MOSH-Insa-Toulouse/2025-2026-4GP-KONIG-EVENSEN/APK_Application/APK_Blocs_Part1.png

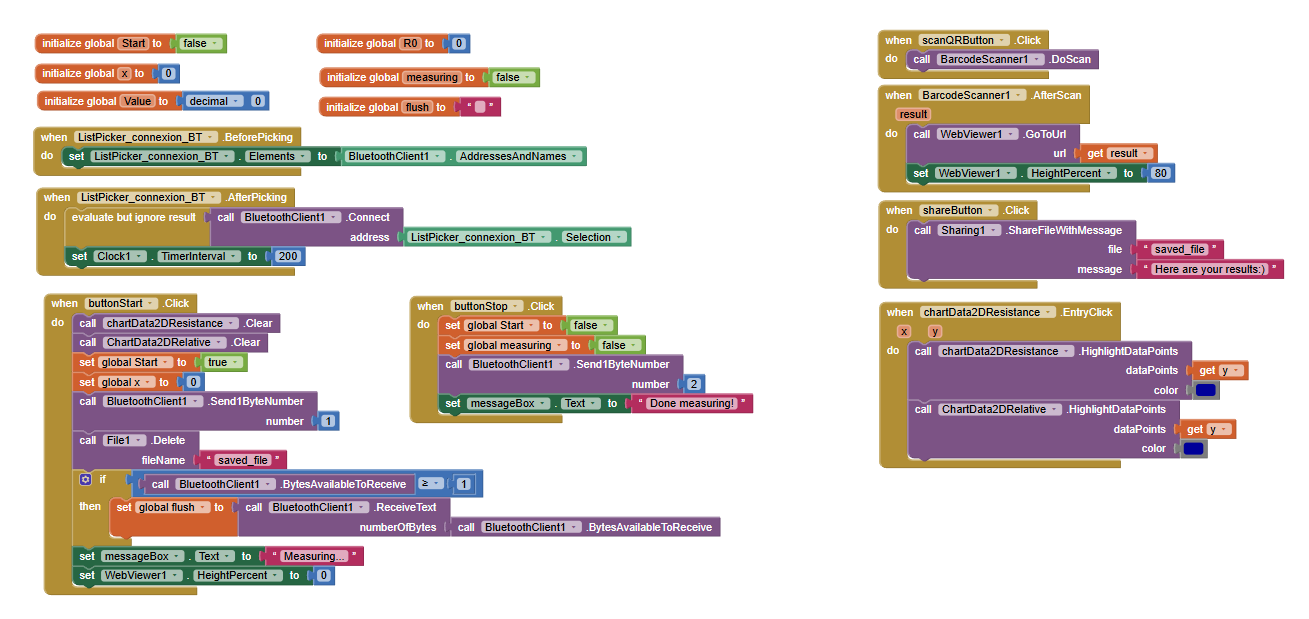
APK_Application/APK_Blocs_Part1.png
