MOSH-Insa-Toulouse/2025-2026-4GP-KONIG-EVENSEN/Photos/APK_Application/Done_Measuring.png

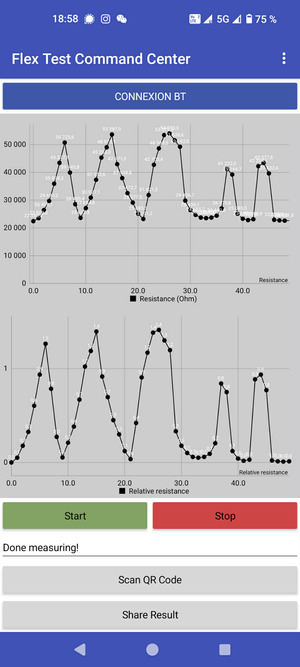
Photos/APK_Application/Done_Measuring.png
