MOSH-Insa-Toulouse/2025-2026-4GP-KONIG-EVENSEN/Photos/Test_Setup/Test_Setup.png

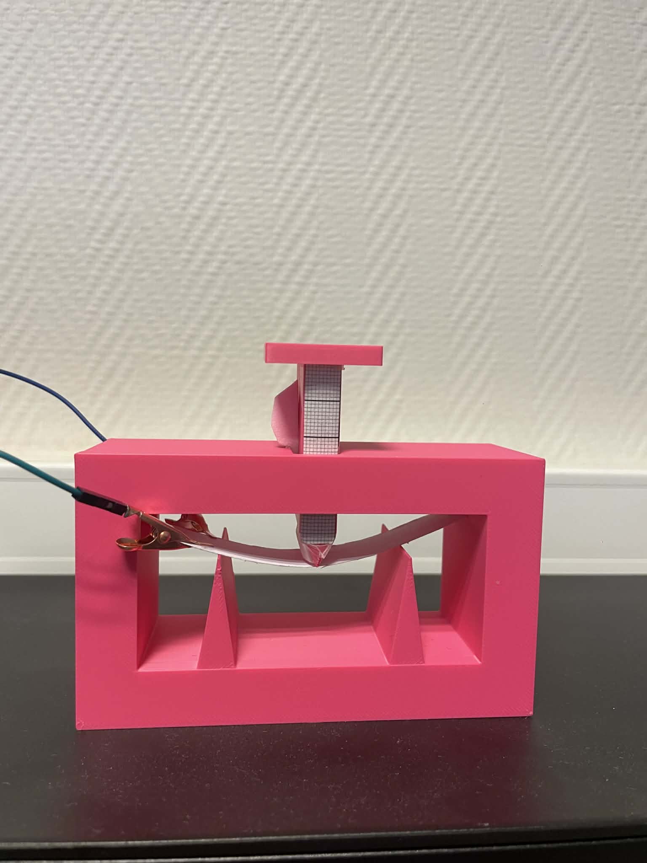
Photos/Test_Setup/Test_Setup.png
