MOSH-Insa-Toulouse/2025-2026-4GP-KONIG-EVENSEN/LTSpice_Files/capteur_arduino.asc

C1: cap; 100n
C2: cap; 100n
C3: cap; 1p
C4: cap; 0.1µ
R1: res; 100k
R2: res; 1k
R3: res; 100k
R5: res; 10k
R6: res; 1k
U1: LTC1050
V1: voltage; 5
V2: voltage; SINE(0 325 50)
V3: voltage; PULSE(0 1 0.2 0.1 0.1 20)
X1: capteur_graphite_A
Named nets: 0, ADC, Vem
.tran 2
