MOSH-Insa-Toulouse/2025-2026-4GP-KONIG-EVENSEN/LTSpice_Files/capteur_graphite_A.asc

B1: bi; I=V(cp,cn)*(10n+V(gc,gn)*10n)
C1: cap; 200µ
R1: res; 1k
Named nets: gp, gc, gn, cp, cn
