MOSH-Insa-Toulouse/2025-2026-4GP-KONIG-EVENSEN/Arduino_Code/QR.cpp

#include "QR.h"

const unsigned char epd_bitmap_frame [] PROGMEM = {0xff, 0xff, 0xff, 0xff, 0xff, 0xff, 0xff, 0xff, 0xff, 0xff, 0xff, 0xff, 0xff, 0xff, 0xff, 0xff, 
	0xff, 0xff, 0xff, 0xff, 0xff, 0xff, 0xff, 0xff, 0xff, 0xff, 0xff, 0xff, 0xff, 0xff, 0xff, 0xff, 
	0xff, 0xff, 0xff, 0xff, 0xff, 0xff, 0xff, 0xff, 0xff, 0xff, 0xff, 0xff, 0xff, 0xff, 0xff, 0xff, 
	0xff, 0xff, 0xff, 0xff, 0xff, 0xff, 0xff, 0xff, 0xff, 0xff, 0xff, 0xff, 0xff, 0xff, 0xff, 0xff, 
	0xff, 0xff, 0xff, 0xff, 0xff, 0xff, 0xff, 0xff, 0xff, 0xff, 0xff, 0xff, 0xff, 0xff, 0xff, 0xff, 
	0xff, 0xff, 0xff, 0xff, 0xff, 0xff, 0xff, 0xff, 0xff, 0xff, 0xff, 0xff, 0xff, 0xff, 0xff, 0xff, 
	0xff, 0xff, 0xff, 0xff, 0xfe, 0x00, 0x0f, 0xe7, 0xf9, 0xf0, 0x00, 0x7f, 0xff, 0xff, 0xff, 0xff, 
	0xff, 0xff, 0xff, 0xff, 0xfc, 0x00, 0x07, 0xe7, 0xf9, 0xe0, 0x00, 0x3f, 0xff, 0xff, 0xff, 0xff, 
	0xff, 0xff, 0xff, 0xff, 0xfc, 0x7f, 0xc7, 0x9f, 0xe7, 0xe3, 0xfe, 0x3f, 0xff, 0xff, 0xff, 0xff, 
	0xff, 0xff, 0xff, 0xff, 0xfc, 0xff, 0xe7, 0x9f, 0xe7, 0xe7, 0xff, 0x3f, 0xff, 0xff, 0xff, 0xff, 
	0xff, 0xff, 0xff, 0xff, 0xfc, 0xe0, 0xe6, 0x79, 0xe0, 0x67, 0x07, 0x3f, 0xff, 0xff, 0xff, 0xff, 
	0xff, 0xff, 0xff, 0xff, 0xfc, 0xc0, 0x66, 0x79, 0xe0, 0x66, 0x03, 0x3f, 0xff, 0xff, 0xff, 0xff, 
	0xff, 0xff, 0xff, 0xff, 0xfc, 0xc0, 0x67, 0xbe, 0xf8, 0x66, 0x03, 0x3f, 0xff, 0xff, 0xff, 0xff, 
	0xff, 0xff, 0xff, 0xff, 0xfc, 0xc0, 0x67, 0x9e, 0x78, 0x66, 0x03, 0x3f, 0xff, 0xff, 0xff, 0xff, 
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
	0xff, 0xff, 0xff, 0xff, 0xfc, 0xce, 0x6f, 0xe6, 0x1e, 0x00, 0x77, 0x3f, 0xff, 0xff, 0xff, 0xff, 
	0xff, 0xff, 0xff, 0xff, 0xfc, 0xce, 0x67, 0xe6, 0x1e, 0x00, 0x33, 0x3f, 0xff, 0xff, 0xff, 0xff, 
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
};
